StuckAtPrototype/MicroBit328/png's/FTDI.png

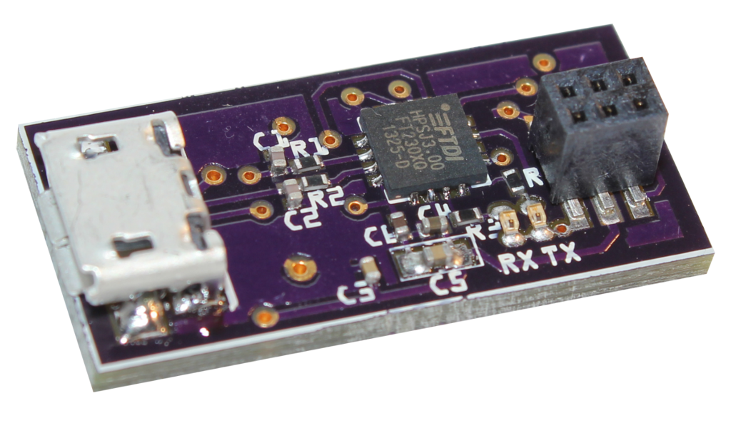
png's/FTDI.png
