StuckAtPrototype/MicroBit328/png's/main image.png

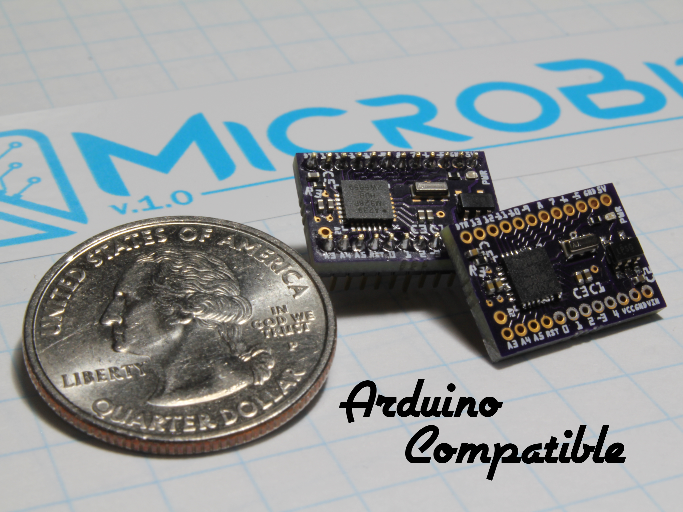
png's/main image.png
