StuckAtPrototype/MicroBit328/png's/time line map.png

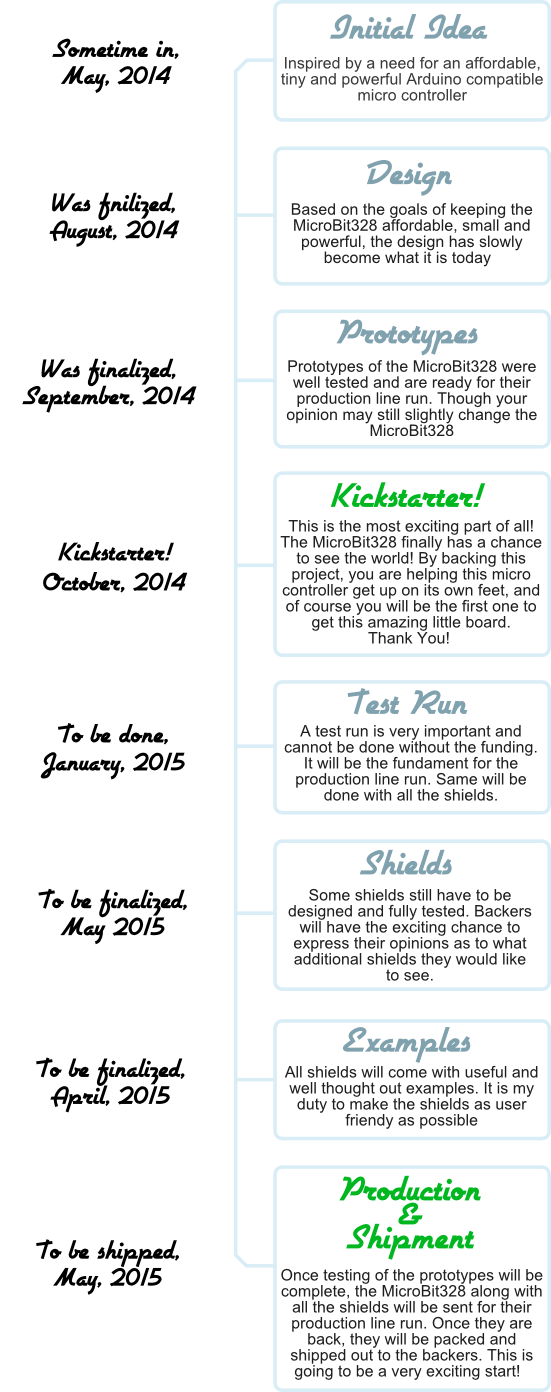
png's/time line map.png
