StuckAtPrototype/MicroBit328/version 0.5 328/Pictures/IMG_0036.JPG

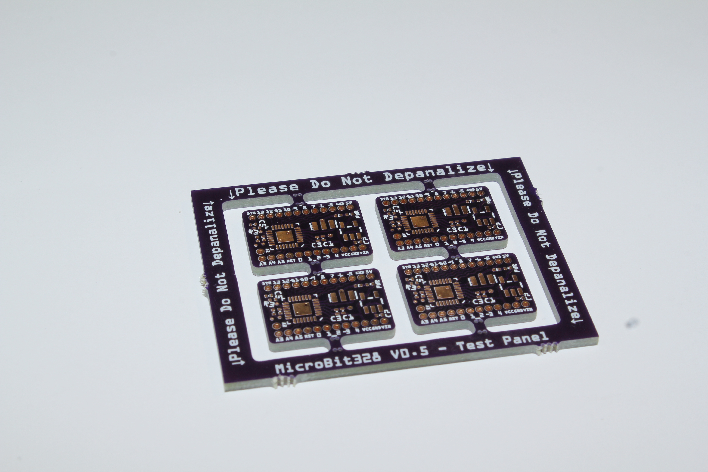
version 0.5 328/Pictures/IMG_0036.JPG
