StuckAtPrototype/MicroBit328/version 0.5 328/Pictures/photo 1(1).JPG

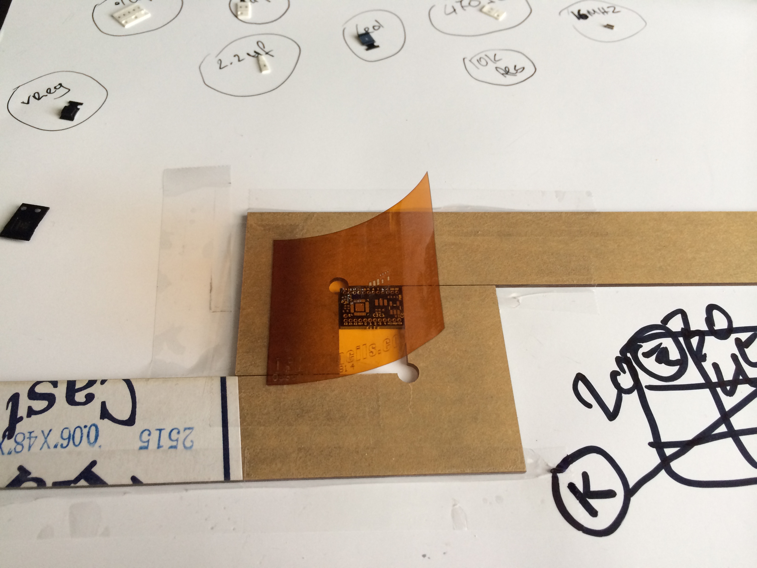
version 0.5 328/Pictures/photo 1(1).JPG
